ukmaker/HarriettAlarm/V1.0/KiCAD/Harriett/Harriett.kicad_sch

## KiCad design V1.0/KiCAD/Harriett/Harriett.kicad_sch (2023-08-24, an earlier design)

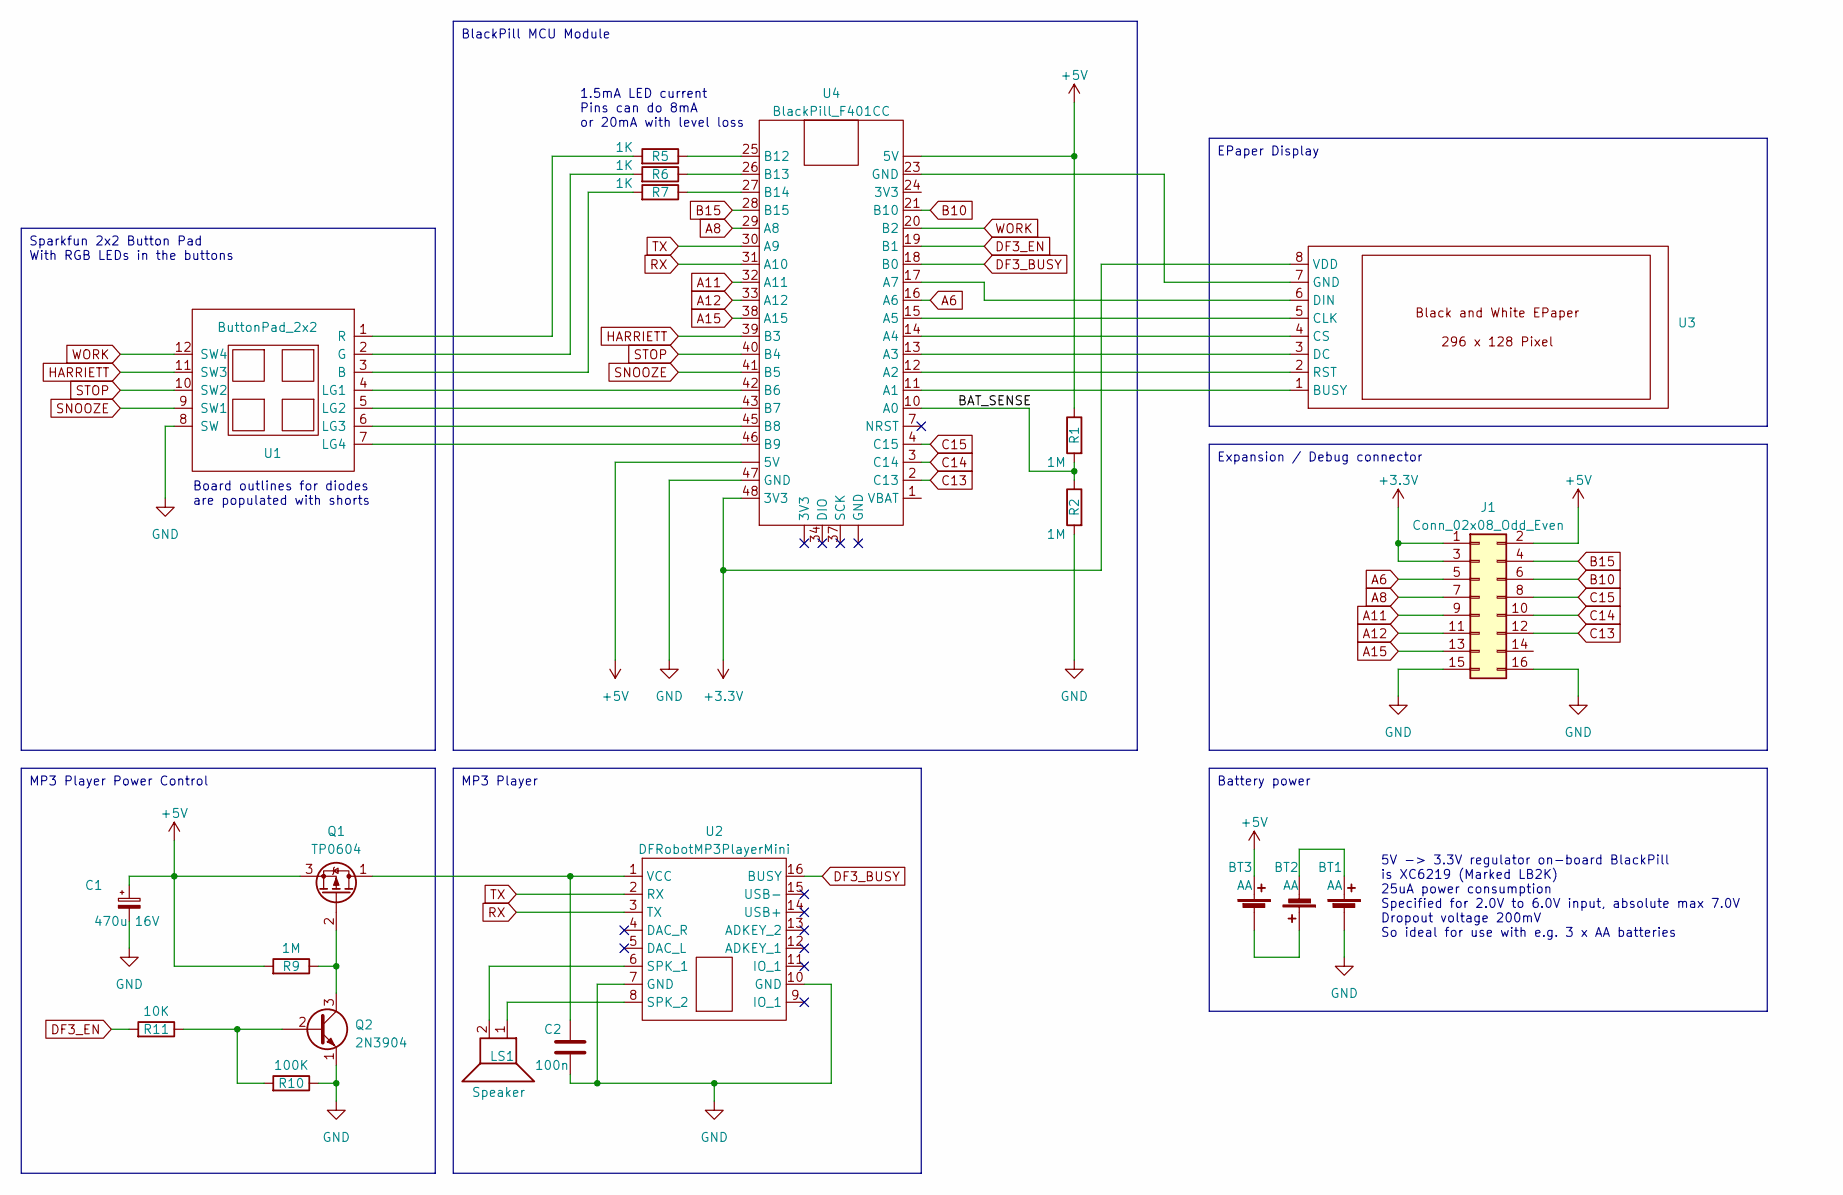
[picture p4: schematic Harriett.kicad_sch]

Parts:
BT1, BT2, BT3: AA
C1: 470u 16V
C2: 100n
J1: Conn_02x08_Odd_Even
LS1: Speaker
Q1: TP0604
Q2: 2N3904
R1, R2, R9: 1M
R5, R6, R7: 1K
R10: 100K
R11: 10K
U1: ButtonPad_2x2
U2: DFRobotMP3PlayerMini
U3: (no value)
U4: BlackPill_F401CC

Connections:
+3.3V: J1.1, J1.3, U3.8 (VDD), U4.48 (3V3)
+5V: BT3.1 (+), C1.1, J1.2, Q1.3 (S), R1.1, R9.2, U4. (3V3)
A6: J1.5, U4.16 (A6)
A8: J1.7, U4.29 (A8)
A11: J1.9, U4.32 (A11)
A12: J1.11, U4.33 (A12)
A15: J1.13, U4.38 (A15)
B10: J1.6, U4.21 (B10)
B15: J1.4, U4.28 (B15)
BAT_SENSE: R1.2, R2.1, U4.10 (A0)
C13: J1.12, U4.2 (C13)
C14: J1.10, U4.3 (C14)
C15: J1.8, U4.4 (C15)
DF3_BUSY: U2.16 (BUSY), U4.18 (B0)
DF3_EN: R11.2, U4.19 (B1)
GND: BT1.2 (-), C1.2, C2.2, J1.15, J1.16, Q2.1 (E), R2.2, R10.1, U1.8 (SW), U2.7 (GND), U2.10 (GND), U4.47 (GND)
HARRIETT: U1.11 (SW3), U4.39 (B3)
unnamed: BT1.1 (+), BT2.2 (-)
unnamed: BT2.1 (+), BT3.2 (-)
unnamed: C2.1, Q1.1 (D), U2.1 (VCC)
unnamed: LS1.1, U2.8 (SPK_2)
unnamed: LS1.2, U2.6 (SPK_1)
unnamed: Q1.2 (G), Q2.3 (C), R9.1
unnamed: Q2.2 (B), R10.2, R11.1
unnamed: R5.1, U4.25 (B12)
unnamed: R5.2, U1.1 (R)
unnamed: R6.1, U4.26 (B13)
unnamed: R6.2, U1.2 (G)
unnamed: R7.1, U4.27 (B14)
unnamed: R7.2, U1.3 (B)
unnamed: U1.4 (LG1), U4.42 (B6)
unnamed: U1.5 (LG2), U4.43 (B7)
unnamed: U1.6 (LG3), U4.45 (B8)
unnamed: U1.7 (LG4), U4.46 (B9)
unnamed: U3.1 (BUSY), U4.11 (A1)
unnamed: U3.2 (RST), U4.12 (A2)
unnamed: U3.3 (DC), U4.13 (A3)
unnamed: U3.4 (CS), U4.14 (A4)
unnamed: U3.5 (CLK), U4.15 (A5)
unnamed: U3.6 (DIN), U4.17 (A7)
unnamed: U3.7 (GND), U4.23 (GND)
RX: U2.3 (TX), U4.31 (A10)
SNOOZE: U1.9 (SW1), U4.41 (B5)
STOP: U1.10 (SW2), U4.40 (B4)
TX: U2.2 (RX), U4.30 (A9)
WORK: U1.12 (SW4), U4.20 (B2)

Notes on the sheet:
EPaper Display
MP3 Player Power Control
Expansion / Debug connector
Sparkfun 2x2 Button Pad With RGB LEDs in the buttons
Battery power
MP3 Player
BlackPill MCU Module
Board outlines for diodes are populated with shorts
1.5mA LED current Pins can do 8mA or 20mA with level loss
5V -> 3.3V regulator on-board BlackPill is XC6219 (Marked LB2K) 25uA power consumption Specified for 2.0V to 6.0V input, absolute max 7.0V Dropout voltage 200mV So ideal for use with e.g. 3 x AA batteries
