ukmaker/HarriettAlarm/V1.0/PlatformIO/HarriettAlarm/src/harriett.h

#include <avr/pgmspace.h>

static unsigned int harriett_width = 70;
static unsigned int harriett_height = 106;

static unsigned char harriett_bitmap[] PROGMEM = {
	1,1,1,1,1,1,1,1,0,0,0,0,0,0,0,0,
	1,1,1,1,1,1,1,1,1,1,1,1,1,1,1,1,
	1,1,1,1,1,1,1,1,1,1,1,1,1,1,1,1,
	1,1,1,1,1,1,1,1,1,1,1,1,1,1,1,1,
	1,1,1,1,1,1,
	1,1,1,1,1,0,0,0,0,1,1,1,1,1,1,0,
	0,0,0,1,1,1,1,1,1,1,1,1,1,1,1,1,
	1,1,1,1,1,1,1,1,1,1,1,1,1,1,1,1,
	1,1,1,1,1,1,1,1,0,0,0,1,1,1,0,0,
	0,1,1,1,1,1,
	1,1,1,0,0,0,1,1,1,1,1,1,1,1,1,1,
	1,1,0,0,0,1,1,1,1,1,1,1,1,1,1,1,
	1,1,1,1,1,1,1,1,1,1,1,1,1,1,1,1,
	1,1,1,1,1,1,1,1,0,1,1,0,0,0,0,0,
	0,0,0,0,1,1,
	1,1,0,0,1,1,1,1,1,1,1,1,1,1,1,1,
	1,1,1,1,0,0,0,1,1,1,1,1,1,1,1,1,
	1,1,1,1,1,1,1,1,1,1,1,1,1,1,1,1,
	1,1,1,1,1,1,1,0,0,1,1,1,0,0,0,0,
	0,0,0,0,0,1,
	1,0,0,1,1,1,1,1,1,1,1,1,1,1,1,1,
	1,1,1,1,1,1,0,0,0,1,1,1,1,1,1,1,
	1,1,1,1,1,1,1,1,1,1,1,1,1,1,0,0,
	0,0,0,0,0,0,0,0,0,0,1,1,1,0,0,0,
	1,1,0,0,0,0,
	1,0,1,1,1,1,1,1,1,1,1,1,1,1,1,1,
	1,1,1,1,1,1,1,1,0,0,1,1,1,1,1,1,
	1,1,1,1,1,1,1,1,1,1,1,0,0,0,0,1,
	0,0,0,0,0,0,0,0,0,0,0,0,1,1,1,0,
	1,1,1,0,0,1,
	0,0,1,1,1,1,1,1,1,1,1,1,1,1,1,1,
	1,1,1,1,1,1,1,1,1,0,0,1,1,1,1,1,
	1,1,1,1,1,1,1,1,1,1,0,0,1,1,1,1,
	1,1,1,1,1,1,1,1,1,1,0,0,0,1,1,1,
	0,1,1,1,0,0,
	0,0,1,1,1,1,1,1,1,1,1,0,1,1,1,1,
	1,1,1,1,1,1,1,1,1,1,0,1,1,1,1,1,
	1,1,1,1,1,1,1,1,1,0,0,1,1,1,1,1,
	1,1,1,1,1,1,1,1,1,1,1,1,0,0,1,1,
	0,1,1,1,1,0,
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
	};
