ukmaker/HarriettAlarm/V1.0/PlatformIO/HarriettAlarm/src/epaper.h

#ifndef HARRIETT_DISPLAY_H
#define HARRIETT_DISPLAY_H
#define ENABLE_GxEPD2_GFX 0

// uncomment next line to use class GFX of library GFX_Root instead of Adafruit_GFX
//#include <GFX.h>
// Note: if you use this with ENABLE_GxEPD2_GFX 1:
//       uncomment it in GxEPD2_GFX.h too, or add #include <GFX.h> before any #include <GxEPD2_GFX.h>

#include <GxEPD2_BW.h>
#include <Fonts/FreeMonoBold9pt7b.h>
#include <Fonts/FreeMonoBold24pt7b.h>
#include "GxEPD2_display_selection_new_style.h"


#endif
